shubh24321/Bhumi-Drishti/hardware/sensor component/AMS1117-3.3.png

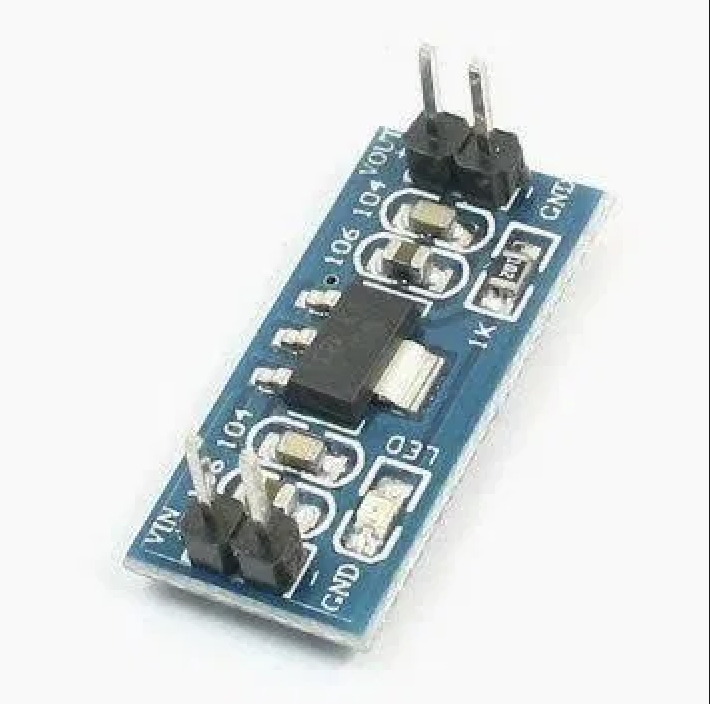
hardware/sensor component/AMS1117-3.3.png
