shubh24321/Bhumi-Drishti/hardware/sensor component/BME280.png

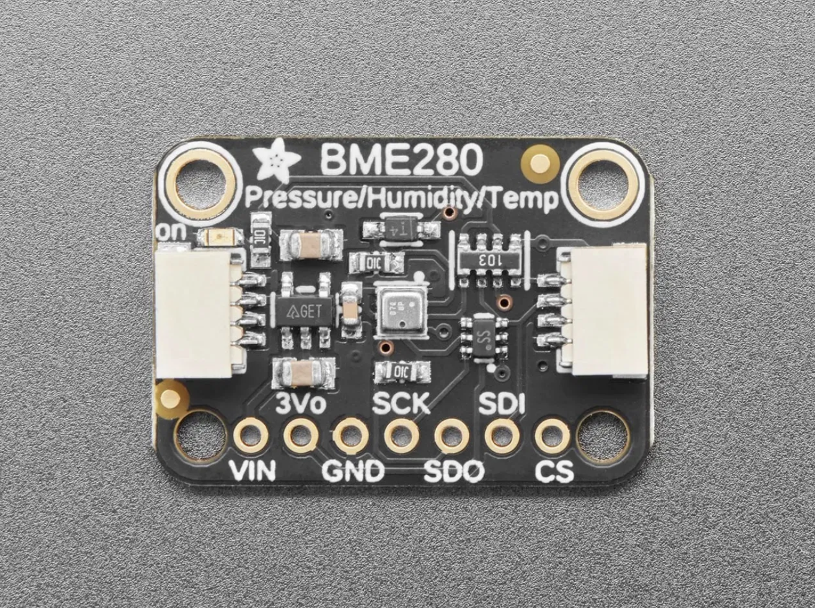
hardware/sensor component/BME280.png
