shubh24321/Bhumi-Drishti/hardware/sensor component/INA219.png

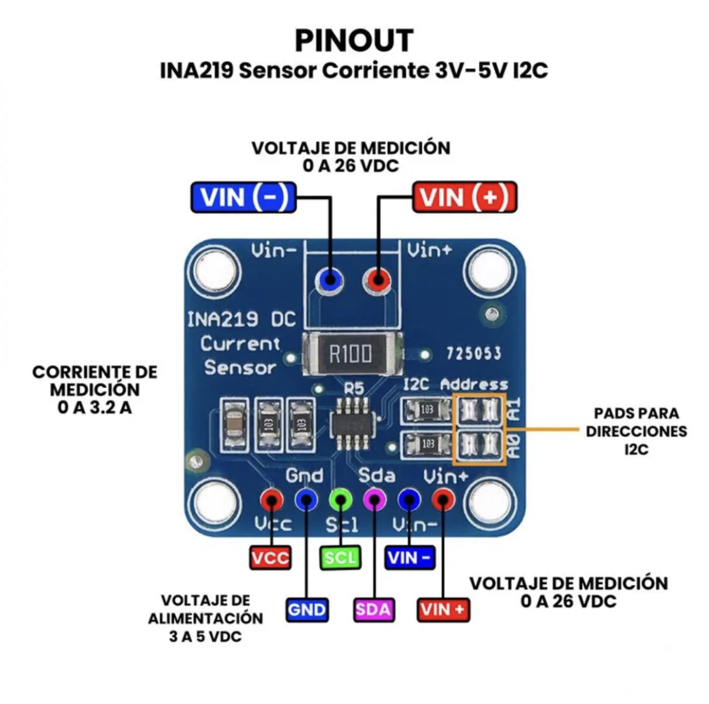
hardware/sensor component/INA219.png
