shubh24321/Bhumi-Drishti/hardware/sensor component/LIS3MDL.png

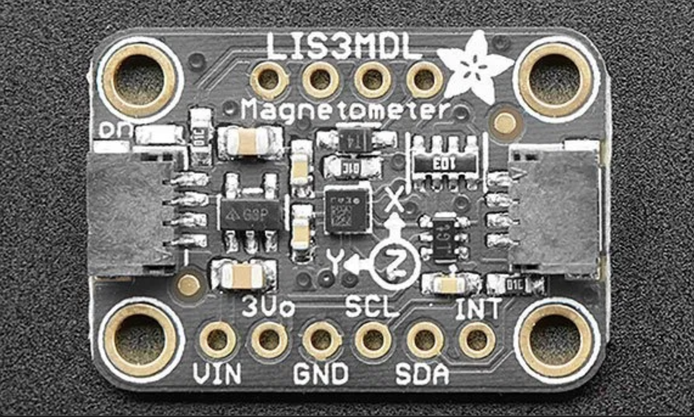
hardware/sensor component/LIS3MDL.png
