shubh24321/Bhumi-Drishti/hardware/sensor component/PCA9548A.png

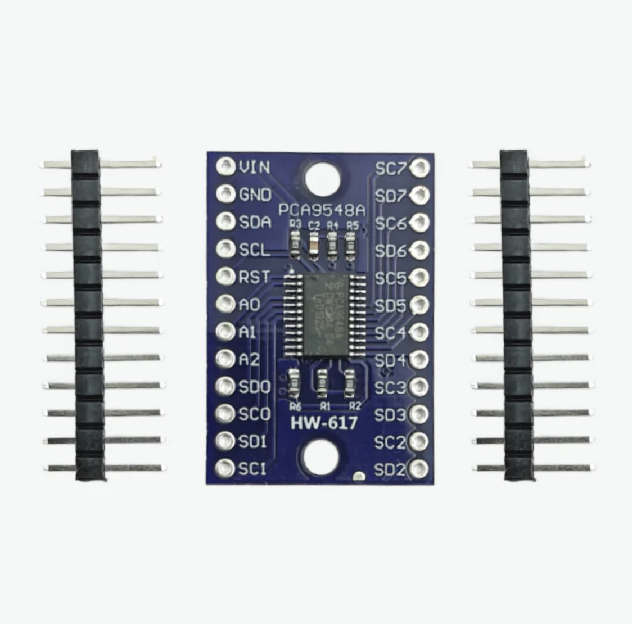
hardware/sensor component/PCA9548A.png
