shubh24321/Bhumi-Drishti/hardware/sensor component/RYLR998.png

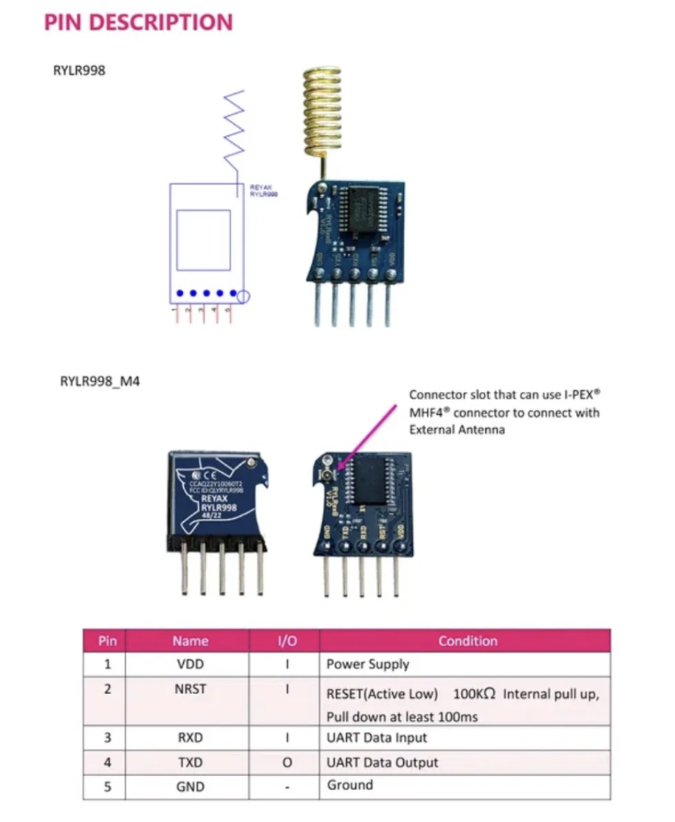
hardware/sensor component/RYLR998.png
