shubh24321/Bhumi-Drishti/hardware/sensor component/TEENSY 4.1 Parts.png

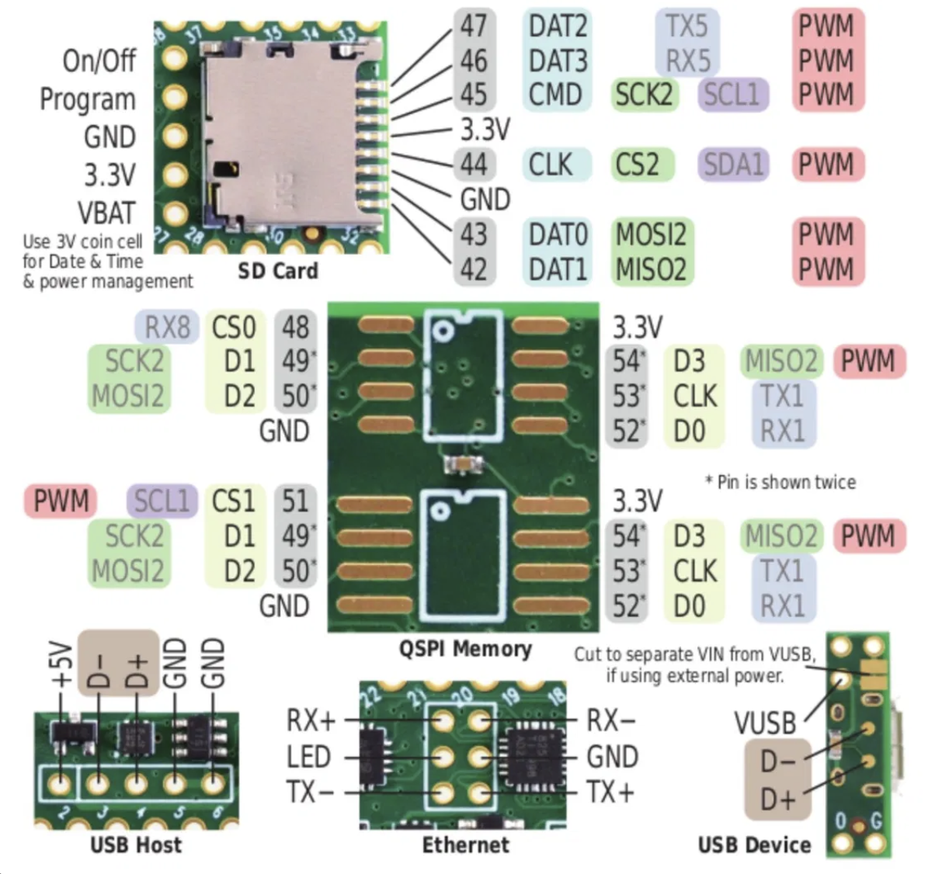
hardware/sensor component/TEENSY 4.1 Parts.png
