shubh24321/Bhumi-Drishti/hardware/sensor component/Teensy 4.1.png

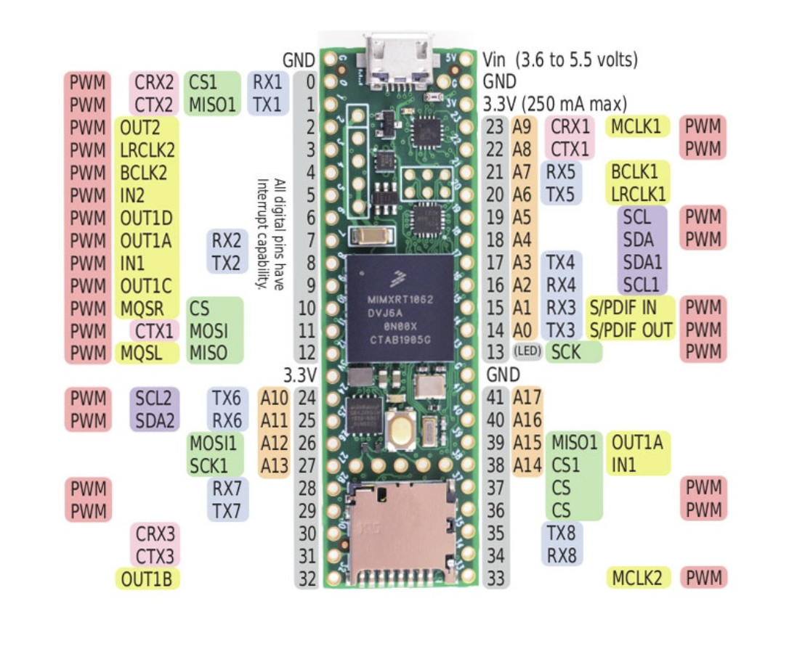
hardware/sensor component/Teensy 4.1.png
