shubh24321/Bhumi-Drishti/hardware/sensor component/TMP36.png

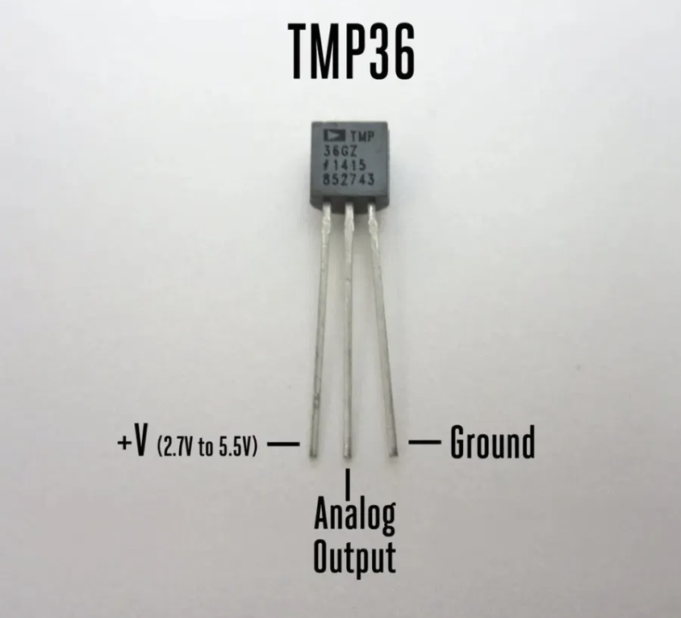
hardware/sensor component/TMP36.png
