shubh24321/Bhumi-Drishti/hardware/sensor component/XL6009.png

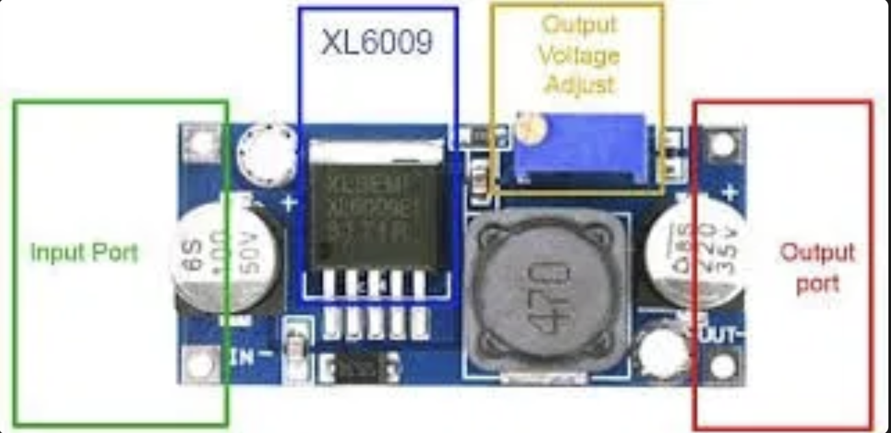
hardware/sensor component/XL6009.png
